ElectronicCats/CatWAN_Relay/Fw/ESP32C6_NFC_SolderingStation/oled_manager.h

#ifndef OLED_MANAGER_H
#define OLED_MANAGER_H

#include <Adafruit_GFX.h>
#include <Adafruit_SSD1306.h>
#include <Arduino.h>
#include <Wire.h>


class OLEDManager {
private:
  Adafruit_SSD1306 display;

public:
  OLEDManager();
  bool begin();

  void showMessage(String msg);
  void showCardAdded(String uid, String name);
  void clear();
  void showWelcome();
  void showWaiting();
  void showWaitingCard();
  void showTimeout();
  void showJSON(const String &json);
  void showCardAdded(const String &uid);
  void showCommand(String cmd);
  void showWelcomeName(String name);
  void showGoodbyeName(String name);
};

#endif
