ElectronicCats/CatWAN_Relay/Fw/ESP32C6_NFC_SolderingStation/feedback_manager.h

#ifndef FEEDBACK_MANAGER_H
#define FEEDBACK_MANAGER_H

#include <Arduino.h>
#include "config.h"

class FeedbackManager {
private:
    int ledGreenPin;
    unsigned long ledOffTime = 0;
    
public:
    FeedbackManager();
    void begin();
    void showSuccess();
    void showError();
    void showWaiting();
    void update();
    void setGreenLED(bool state);
};

#endif // FEEDBACK_MANAGER_H
